youpaw/elec-module/flipper42_cad/subghz.kicad_sch

## KiCad design flipper42_cad/subghz.kicad_sch (2026-06-04)


Parts:
AE1: Antenna 50 Ohm
C51, C81, C101, C121, C122, C123, C124, C125, C131: C,IEC
J1: Conn_Coaxial; 1x02
L121, L122, L123, L131: L,current,IEC
R171: R,IEC
U2: CC1101; QLP20
XTAL: SMD7050-2; Crystal_SMD_7050-2Pin_7.0x5.0mm

Connections:
CSn: U2.7 (NCS)
GDO0: U2.6 (GDO0)
GDO2: U2.3 (GDO2)
unnamed: AE1.1, J1.1 (In)
unnamed: C51.1 (+), U2.5 (DCOUPL)
unnamed: C81.2 (-), U2.8 (XOSC_Q1), XTAL.1
unnamed: C101.2 (-), U2.10 (XOSC_Q2), XTAL.2
unnamed: C121.1 (+), L121.2 (-), U2.12 (RF_P)
unnamed: C121.2 (-), L122.2 (-), L131.1 (+)
unnamed: C122.2 (-), L122.1 (+), L123.2 (-)
unnamed: C123.2 (-), C125.1 (+), L123.1 (+)
unnamed: C124.2 (-), L121.1 (+)
unnamed: C125.2 (-), J1.2 (Ext)
unnamed: C131.1 (+), L131.2 (-), U2.13 (RF_N)
unnamed: R171.1 (+), U2.17 (RBIAS)
P,+: U2.4 (DVDD), U2.9 (AVDD1), U2.11 (AVDD2), U2.14 (AVDD3), U2.15 (AVDD4), U2.18 (DGUARD)
P,GND: C51.2 (-), C81.1 (+), C101.1 (+), C122.1 (+), C123.1 (+), C124.1 (+), C131.2 (-), R171.2 (-), U2.16 (GND1), U2.19 (GND2), U2.DAP (GND3)
SCLK: U2.1 (SCLK)
SI: U2.20 (SI)
SO (GDO1): U2.2 (SO/GDO1)
